Miceuz/rs485-moist-sensor/doc/measurements/reduced.csv

2.130000000000000000e+02
2.110000000000000000e+02
2.090000000000000000e+02
2.100000000000000000e+02
2.110000000000000000e+02
2.100000000000000000e+02
2.110000000000000000e+02
2.100000000000000000e+02
2.110000000000000000e+02
2.100000000000000000e+02
2.120000000000000000e+02
2.110000000000000000e+02
2.120000000000000000e+02
2.110000000000000000e+02
2.100000000000000000e+02
2.090000000000000000e+02
2.100000000000000000e+02
2.090000000000000000e+02
2.100000000000000000e+02
2.090000000000000000e+02
2.080000000000000000e+02
2.070000000000000000e+02
2.080000000000000000e+02
2.090000000000000000e+02
2.080000000000000000e+02
2.090000000000000000e+02
2.080000000000000000e+02
2.090000000000000000e+02
2.080000000000000000e+02
2.090000000000000000e+02
2.100000000000000000e+02
2.080000000000000000e+02
2.150000000000000000e+02
2.100000000000000000e+02
2.110000000000000000e+02
2.100000000000000000e+02
2.090000000000000000e+02
2.080000000000000000e+02
2.090000000000000000e+02
2.080000000000000000e+02
2.070000000000000000e+02
2.120000000000000000e+02
2.100000000000000000e+02
2.080000000000000000e+02
2.090000000000000000e+02
2.080000000000000000e+02
2.090000000000000000e+02
2.110000000000000000e+02
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
