Miceuz/rs485-moist-sensor/src/thermistor.py

import numpy as np
from matplotlib.pyplot import *

resistances = np.array([
68.237,
53.650,
42.506,
33.892,
27.219,
22.021,
17.926,
14.674,
12.081,
10.000,
8.315,
6.948,
5.834,
4.917,
4.161,
3.535,
3.014,
2.586,
2.228,
1.925,
1.669,
1.452])

temperatures = np.array([
-20,
-15,
-10,
-5,
0,
5,
10,
15,
20,
25,
30,
35,
40,
45,
50,
55,
60,
65,
70,
75,
80,
85])

resistances = resistances * 1000
lsb = resistances / (resistances + 10e3) * 1023


#x*x*x*-2.51190730e-07 + x*x*4.33662342e-04 +  x*-3.46093150e-01 + 1.21775339e+02

#x * (x*x*-2.51190730e-07 + x*4.33662342e-04 -3.46093150e-01) + 1.21775339e+02
#x * (x * (x * -2.51190730e-07 + 4.33662342e-04) -3.46093150e-01) + 1.21775339e+02

x*x*x*-2.51190730e-07 + x*x*4.33662342e-04 +  x*-3.46093150e-01 + 1.21775339e+02
def pp(x):
	return x*x*x*-2511/10000000000 + x*x*4336623/10000000000 + x * -346093150/1000000000 + 122
